daviecheng/posture_corrector/images/device_charging.jpg

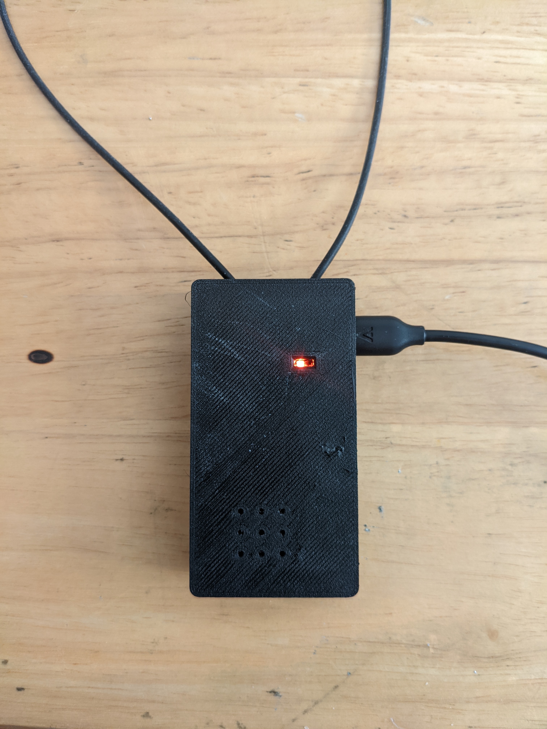
images/device_charging.jpg
