daviecheng/posture_corrector/images/device_enclosure_front.jpg

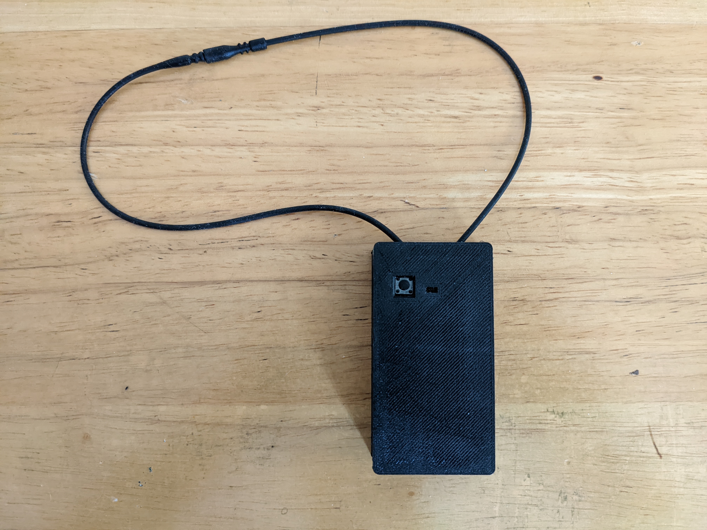
images/device_enclosure_front.jpg
