daviecheng/posture_corrector/images/device_enclosure_side.jpg

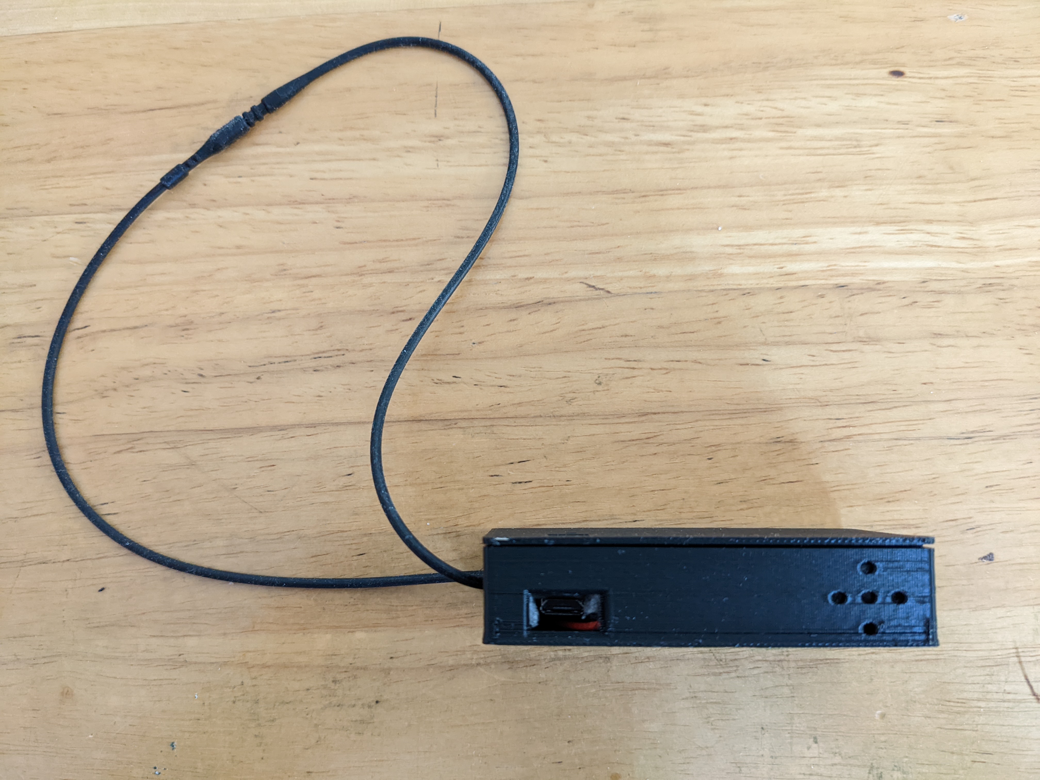
images/device_enclosure_side.jpg
